Batterhead221/scream_bean/Outputs/IMG/SCHEMATIC.png

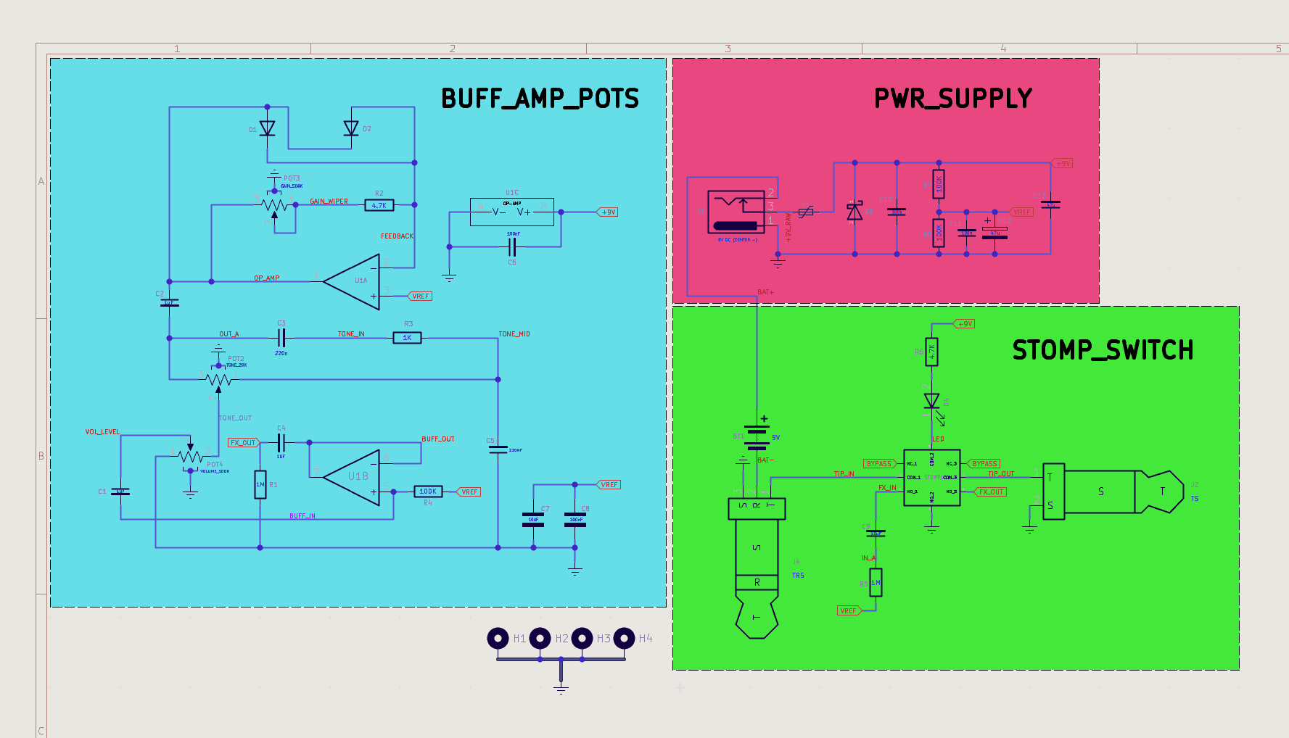
Outputs/IMG/SCHEMATIC.png
